loganw023/wheatboard/Images/image-1.png

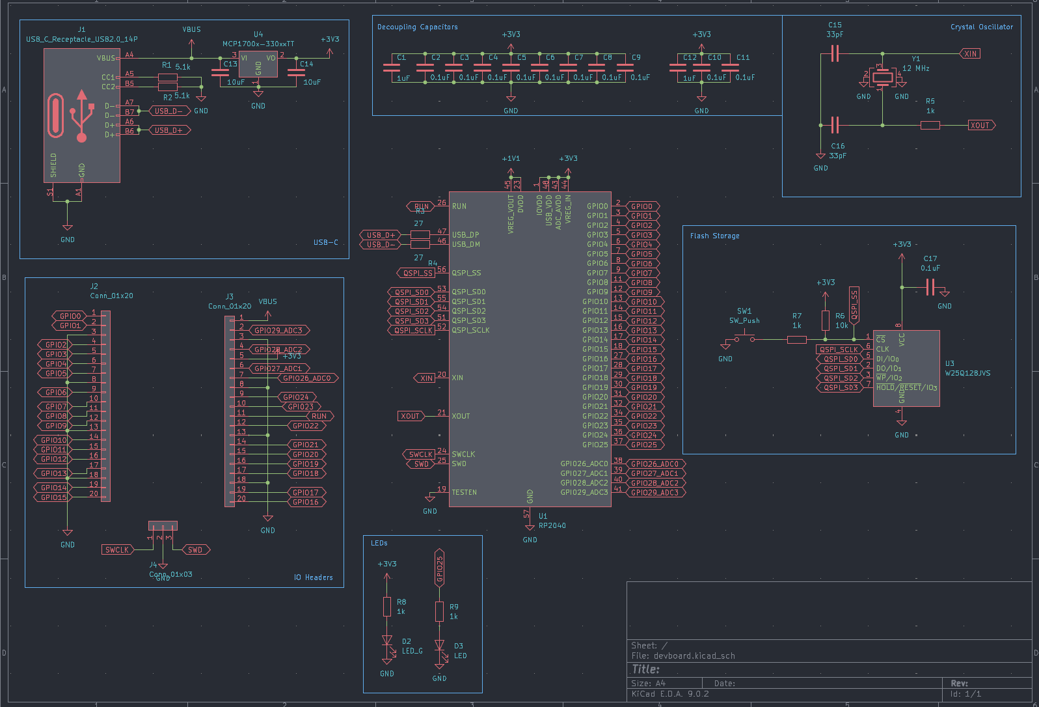
Images/image-1.png
