loganw023/wheatboard/Images/image-4.png

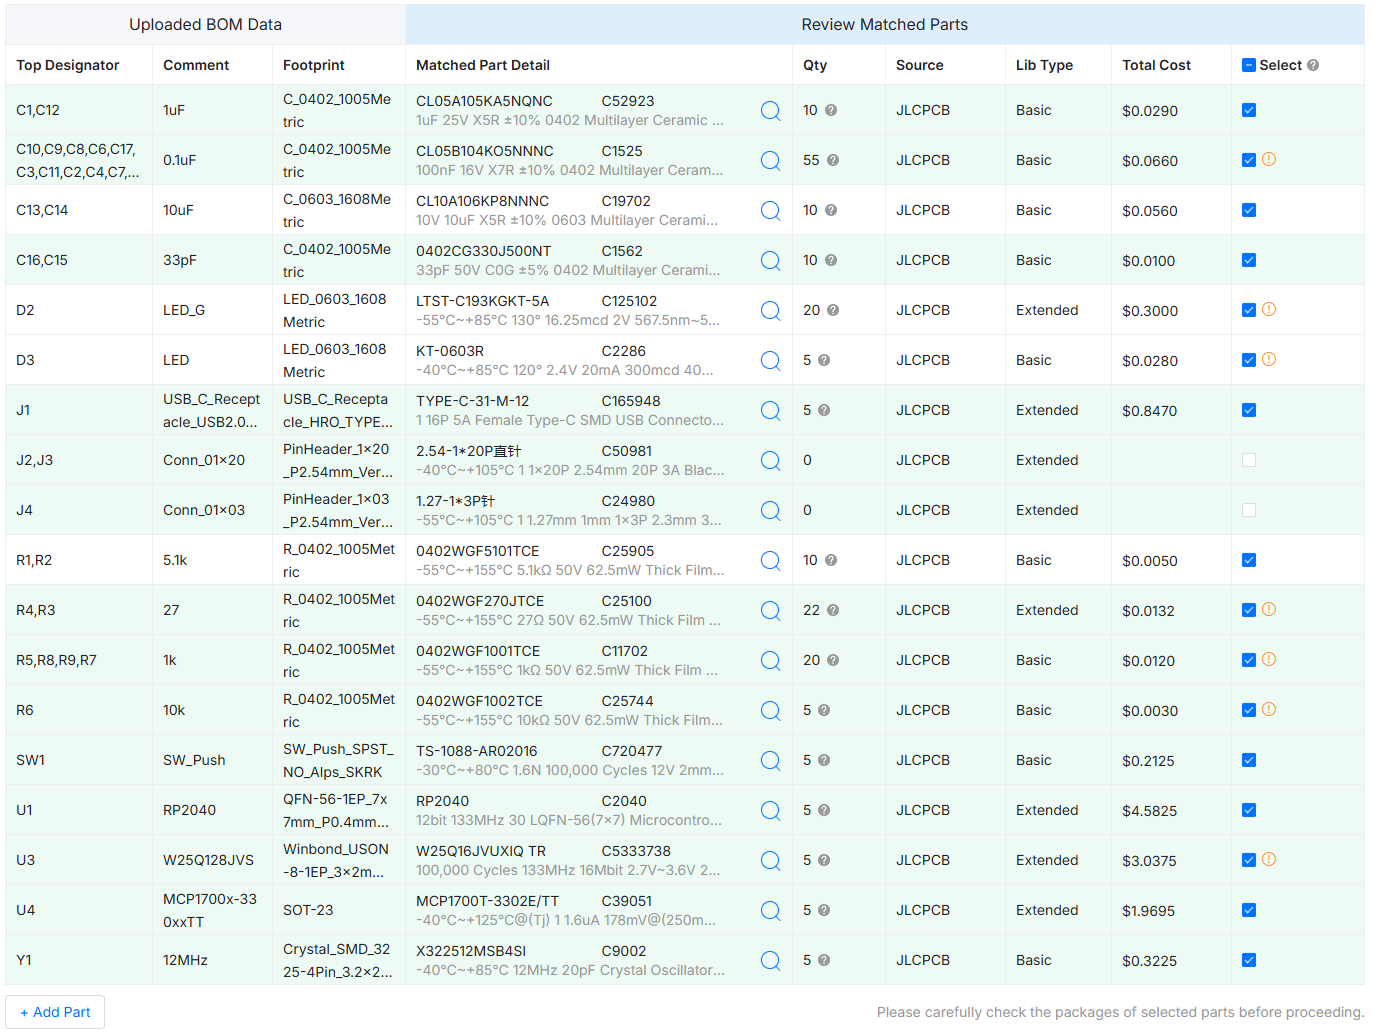
Images/image-4.png
