loganw023/wheatboard/Images/image-5.png

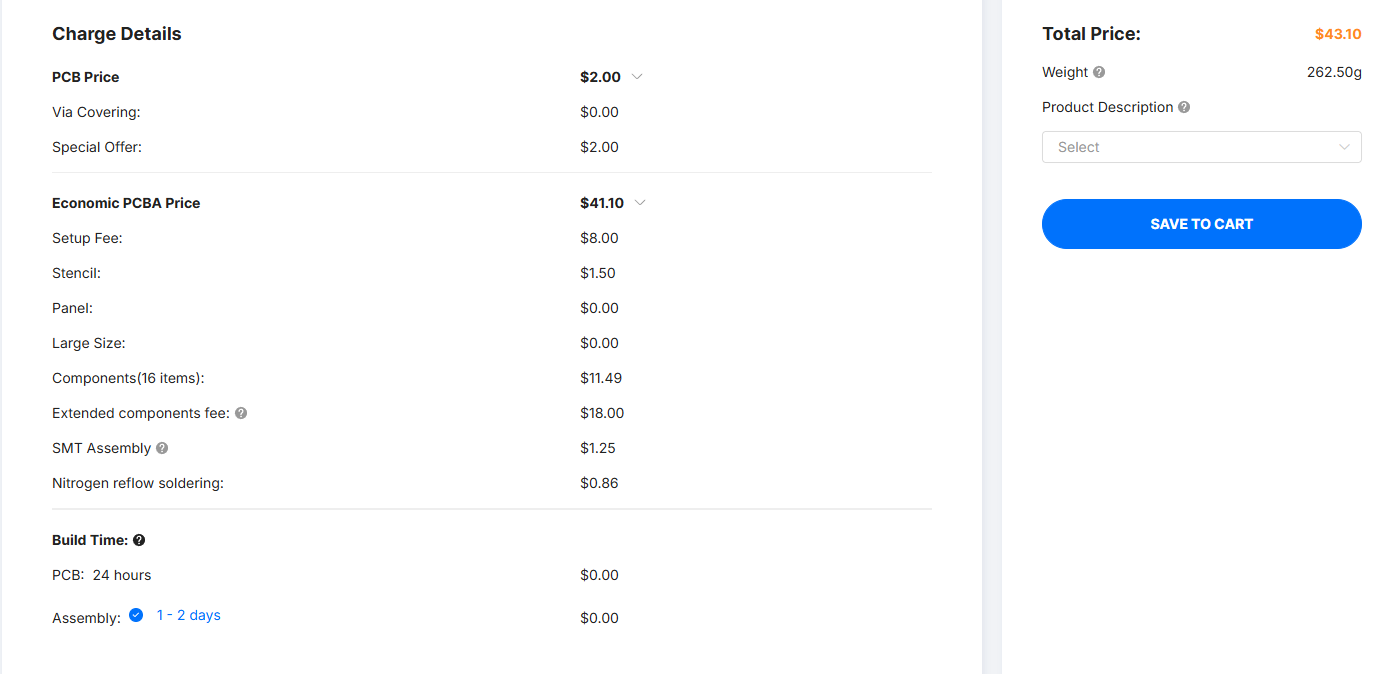
Images/image-5.png
