loganw023/wheatboard/Images/image-6.png

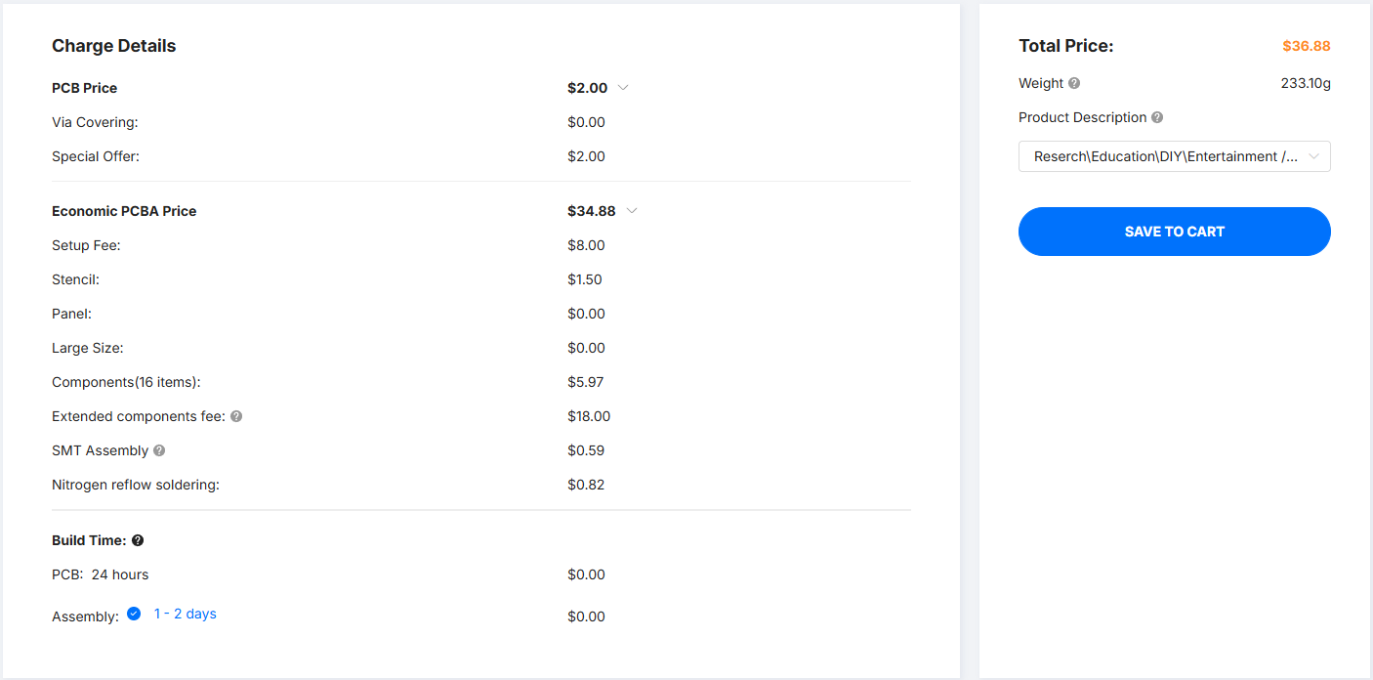
Images/image-6.png
